heligone/picolimno-mkr/doc/20180411_143135.jpg

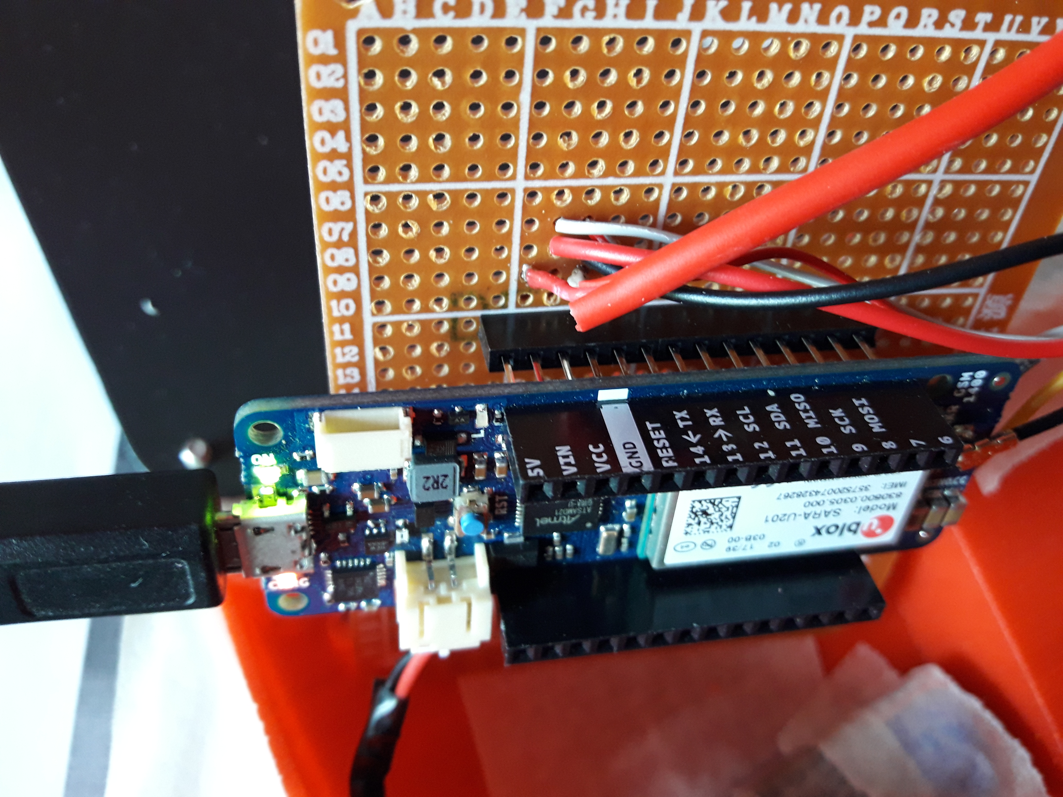
doc/20180411_143135.jpg
