heligone/picolimno-mkr/doc/20180411_143151.jpg

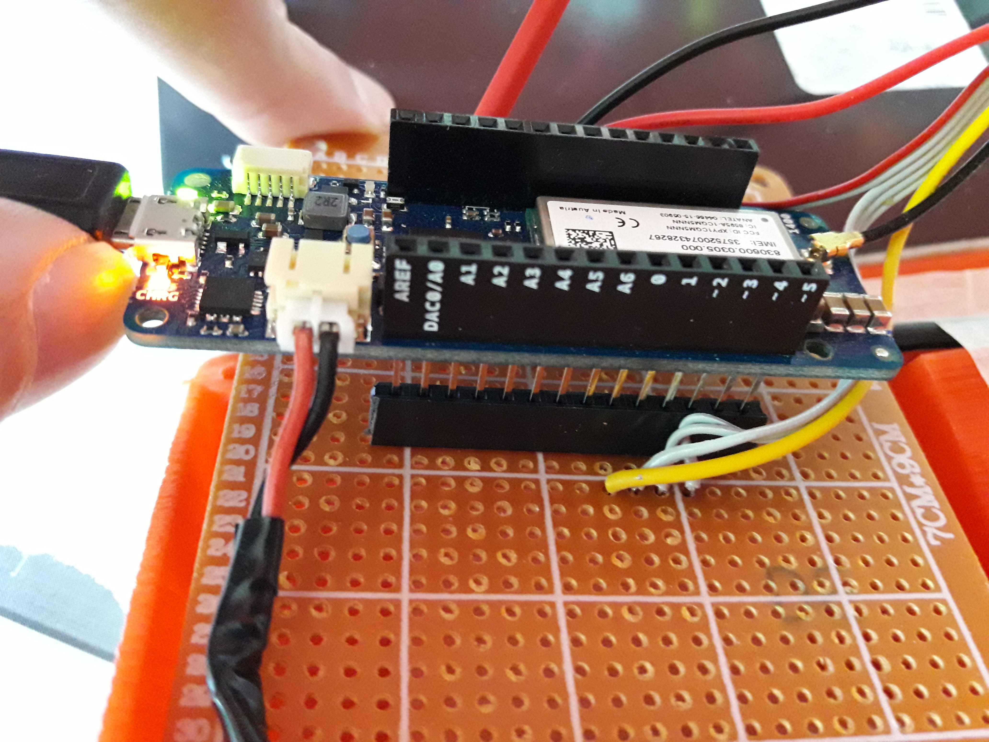
doc/20180411_143151.jpg
