heligone/picolimno-mkr/doc/20180411_143222.jpg

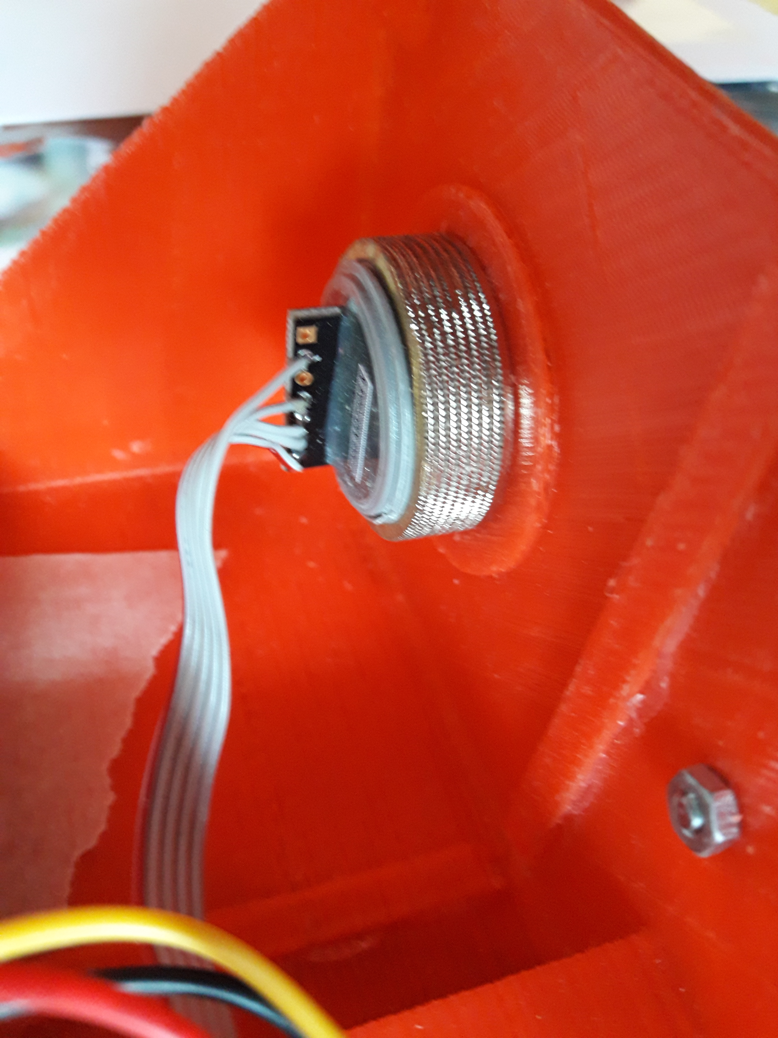
doc/20180411_143222.jpg
